chrissavage2300/Bench-Top-Power-Supply/pics/20260101_194244.jpg

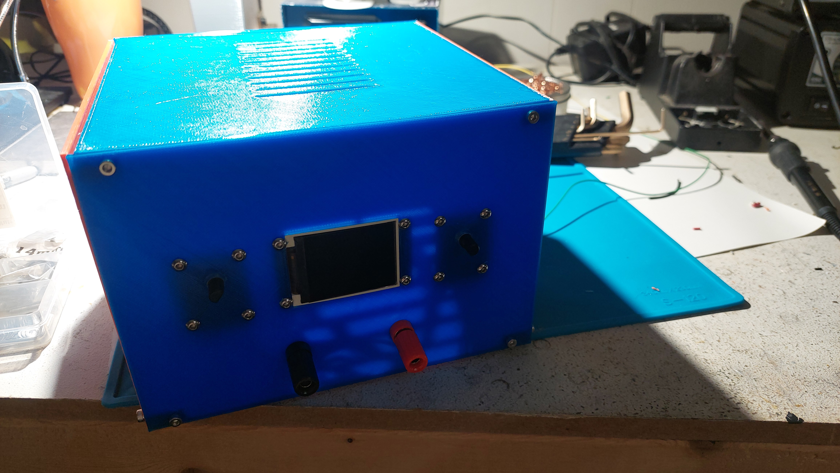
pics/20260101_194244.jpg
