chrissavage2300/Bench-Top-Power-Supply/pics/20260101_194826.jpg

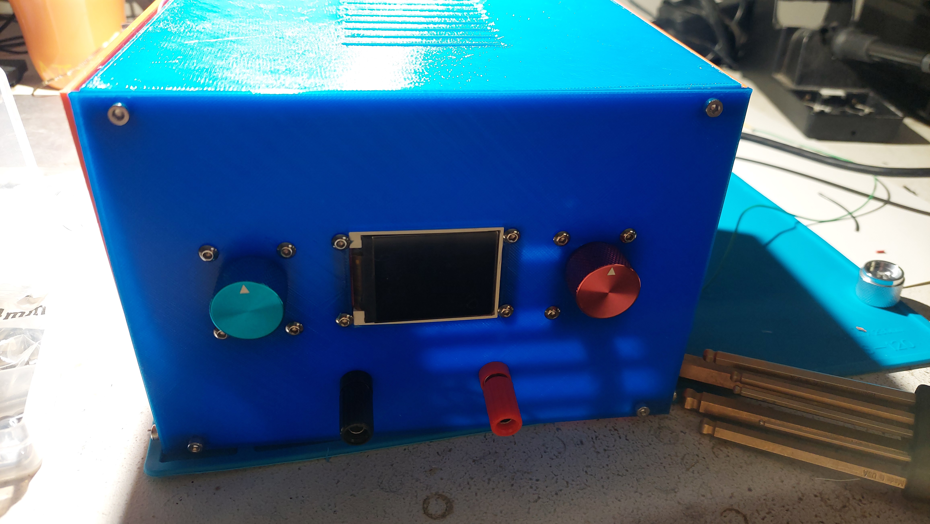
pics/20260101_194826.jpg
