chrissavage2300/Bench-Top-Power-Supply/pics/20260101_195006.jpg

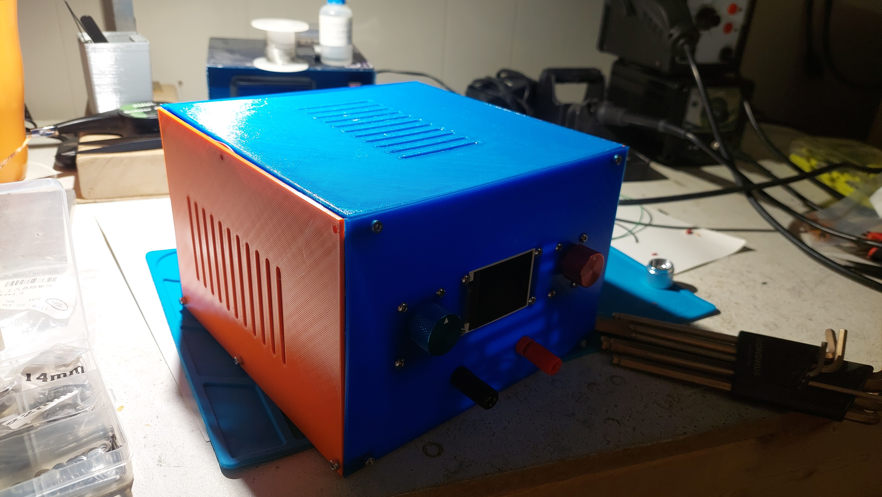
pics/20260101_195006.jpg
