chrissavage2300/Bench-Top-Power-Supply/pics/20260423_074035.jpg

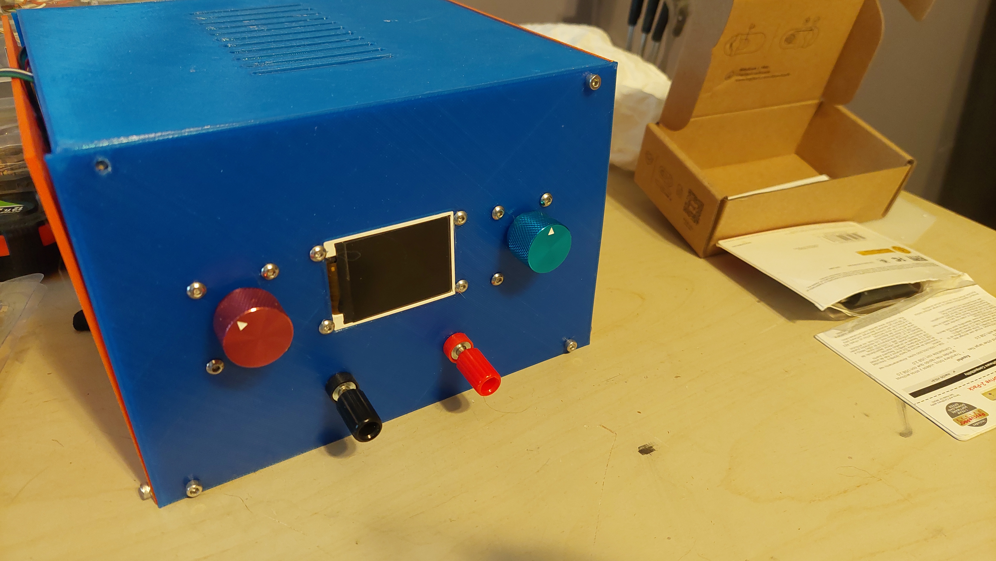
pics/20260423_074035.jpg
